Randomblock1/usb-c-to-c-power-mod-6pin/USB-C-to-C Power Mod.kicad_sch

## KiCad design USB-C-to-C Power Mod.kicad_sch (2023-01-27)

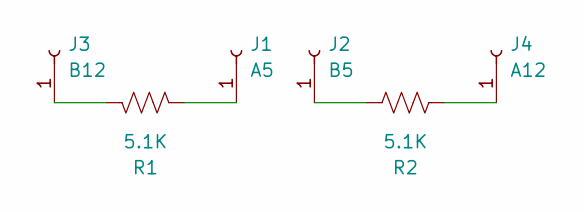
[picture p2: schematic USB-C-to-C Power Mod.kicad_sch]

Parts:
J1: A5; Plated_Hole_D0.3mm
J2: B5; Plated_Hole_D0.3mm
J3: B12; Plated_Hole_D0.3mm
J4: A12; Plated_Hole_D0.3mm
R1, R2: 5.1K; R_0402_1005Metric_Pad0.72x0.64mm_HandSolder

Connections:
unnamed: J1.1, R1.2
unnamed: J2.1, R2.1
unnamed: J3.1, R1.1
unnamed: J4.1, R2.2
